mtomazella/Handy/BD/Diagrama/Handy.jpg

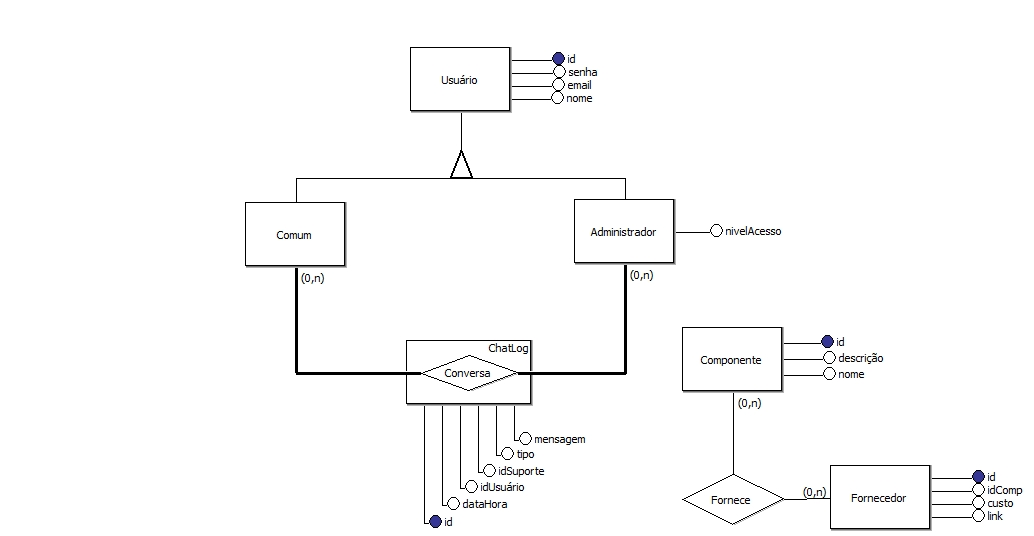
BD/Diagrama/Handy.jpg
