mtomazella/Handy/Documentação/Canvas/Canvas_-_Handy.vpd.png

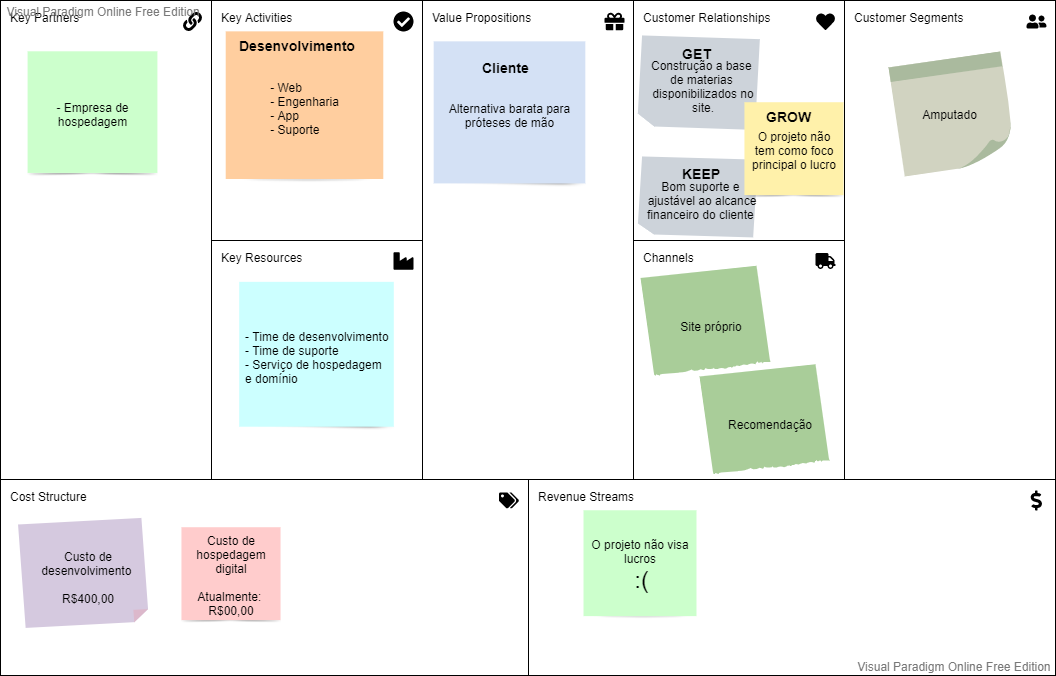
Documentação/Canvas/Canvas_-_Handy.vpd.png
