mtomazella/Handy/Documentação/Casos de Uso/Casos de Uso Mobile-Eng-1.jpg

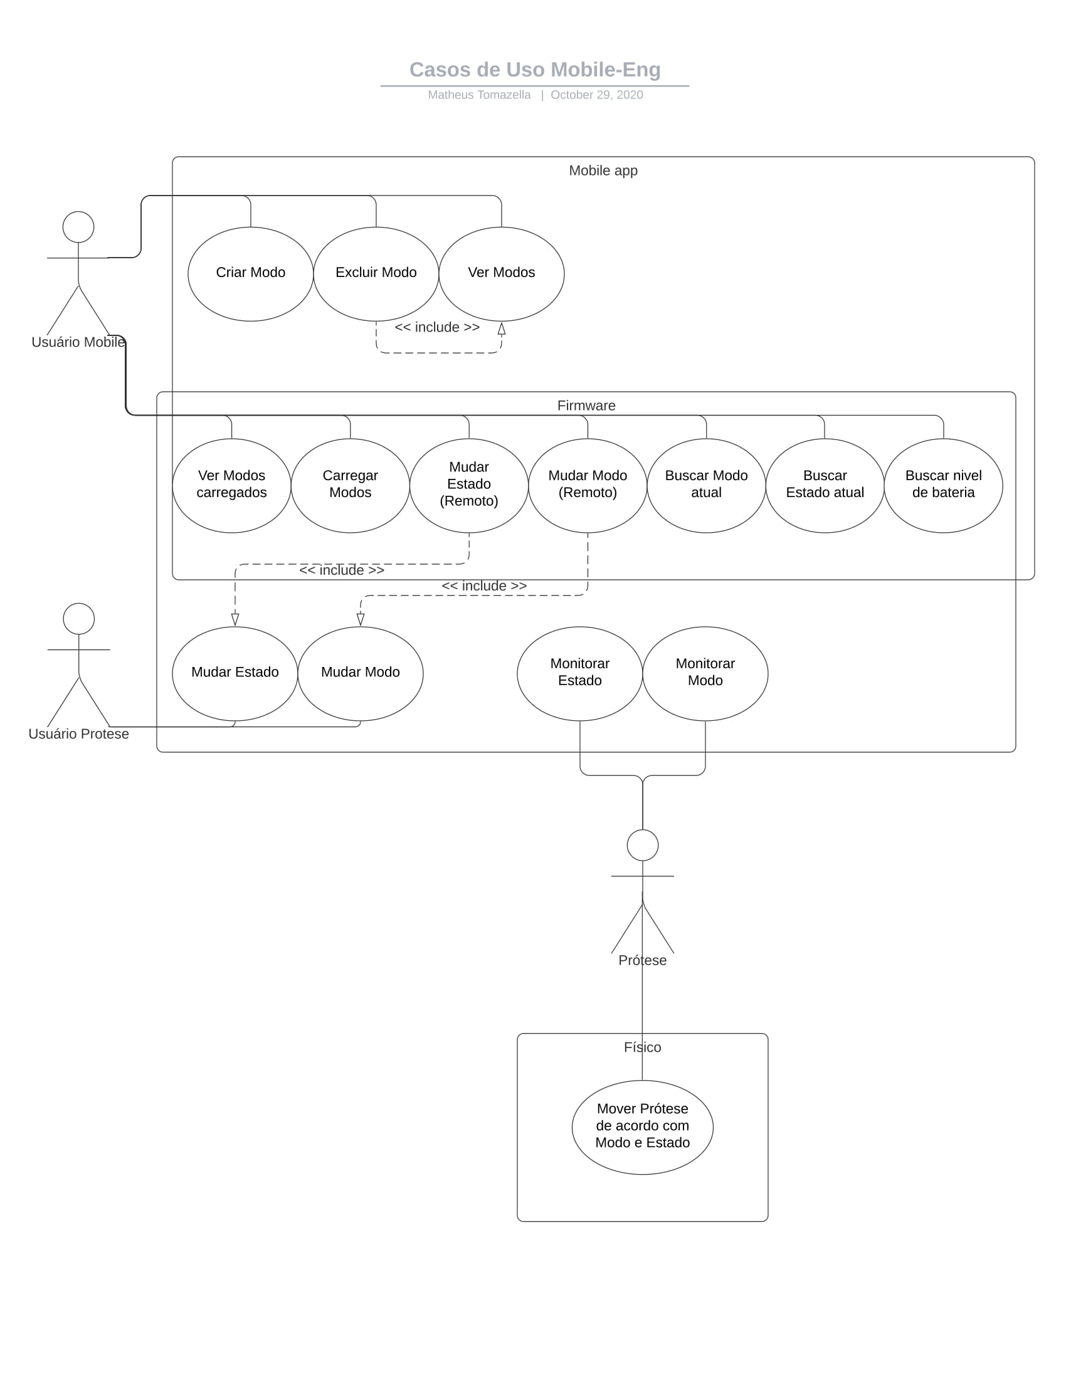
Documentação/Casos de Uso/Casos de Uso Mobile-Eng-1.jpg
