mtomazella/Handy/Documentação/Casos de Uso/Casos de Uso Web-Desktop-1.jpg

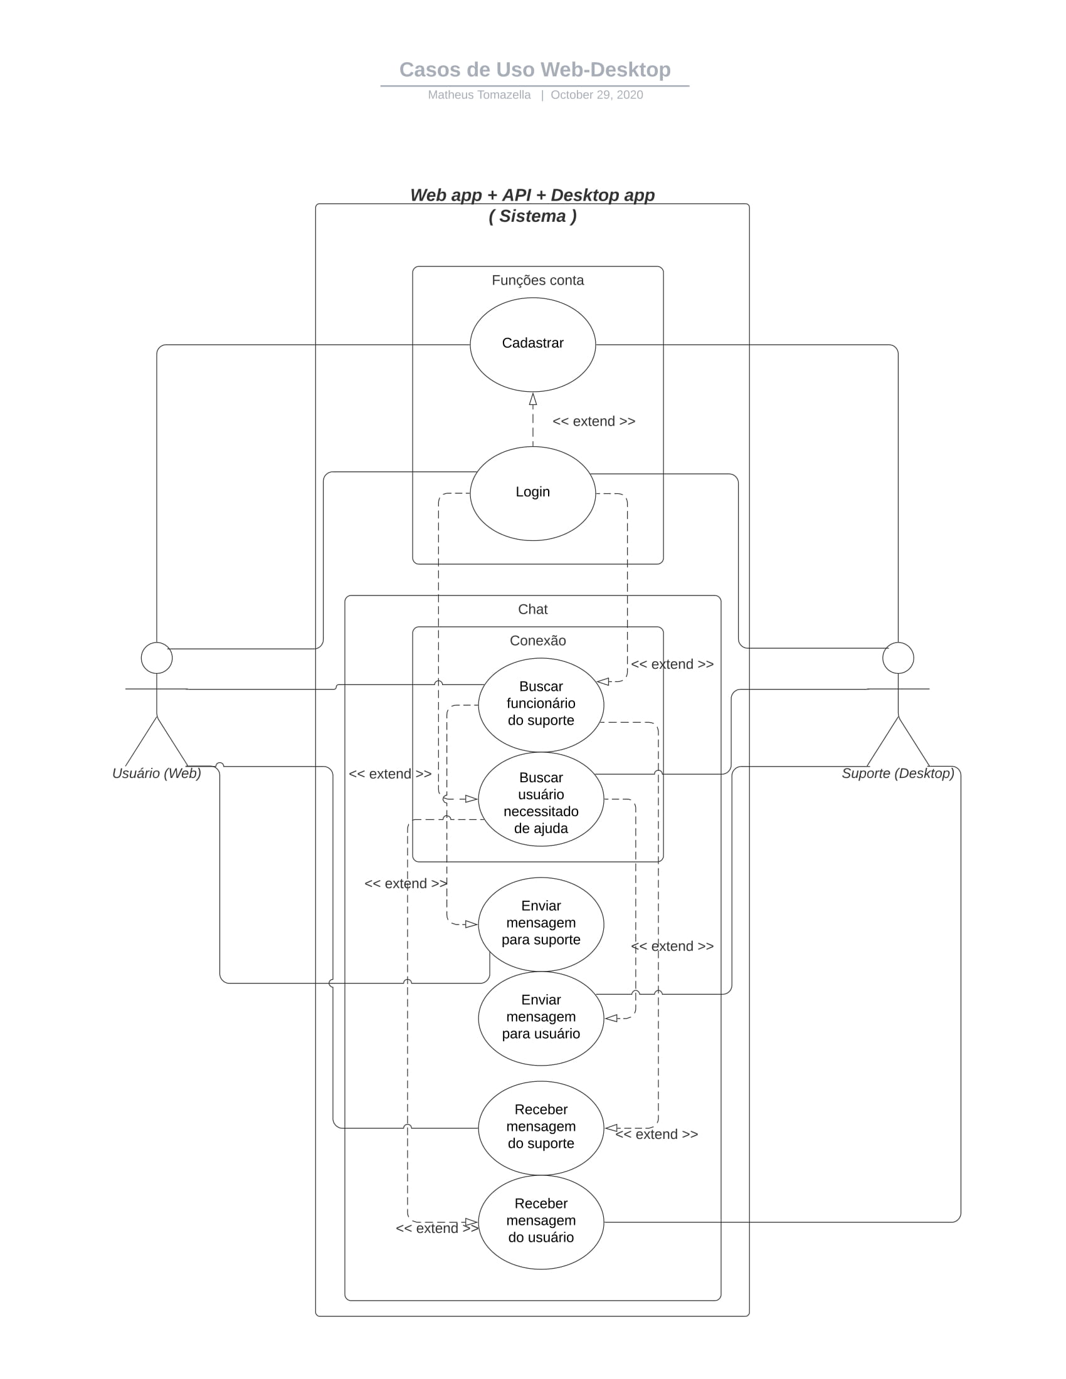
Documentação/Casos de Uso/Casos de Uso Web-Desktop-1.jpg
