mtomazella/Handy/Documentação/Cronograma/Cronograma.jpg

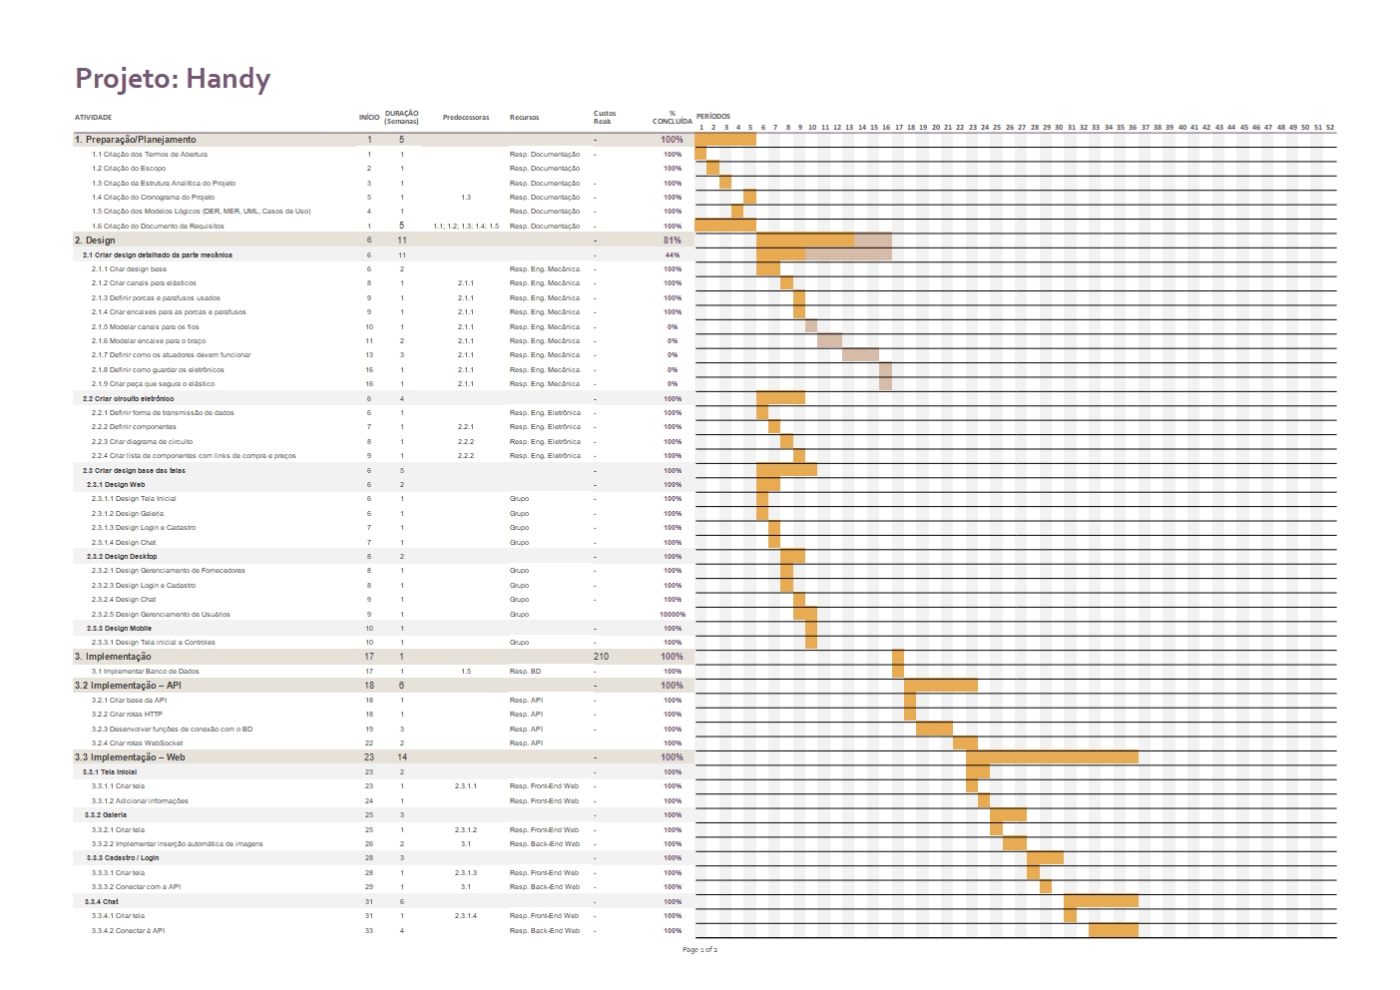
Documentação/Cronograma/Cronograma.jpg
