mtomazella/Handy/Documentação/Desenhos/Baterias.png

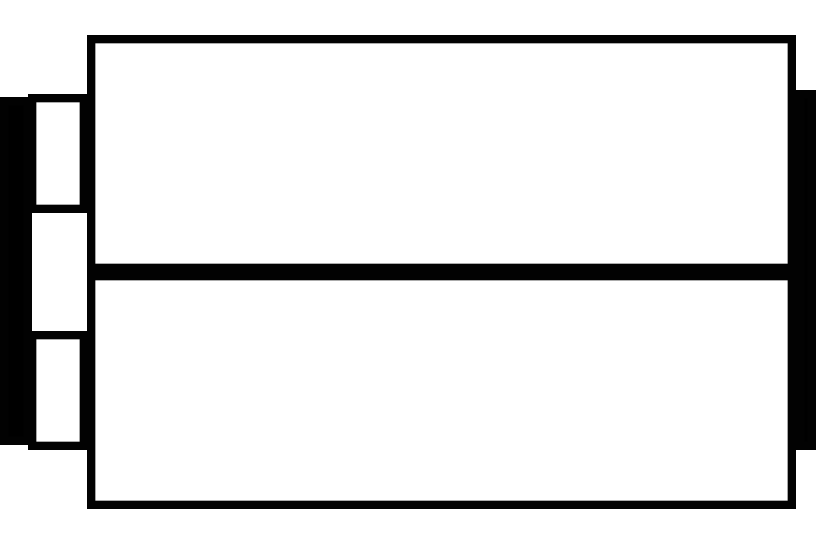
Documentação/Desenhos/Baterias.png
