mtomazella/Handy/Documentação/Desenhos/Handy.png

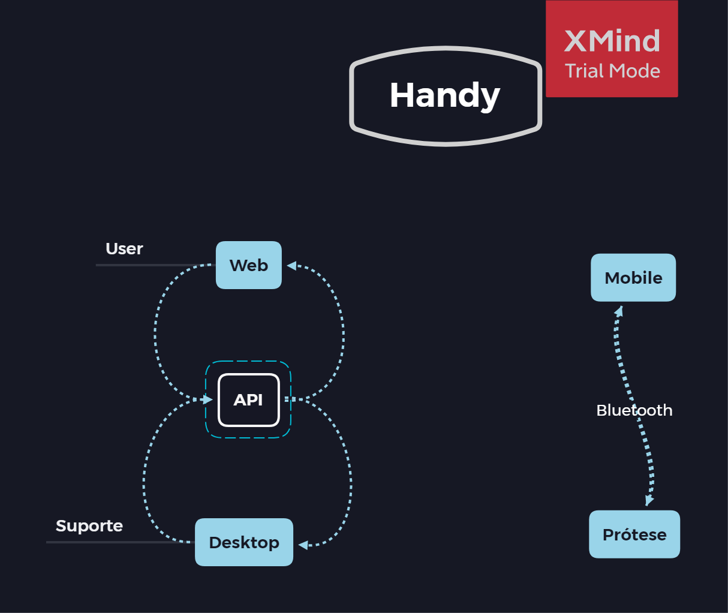
Documentação/Desenhos/Handy.png
