mtomazella/Handy/Documentação/Desenhos/PalmaSketch.png

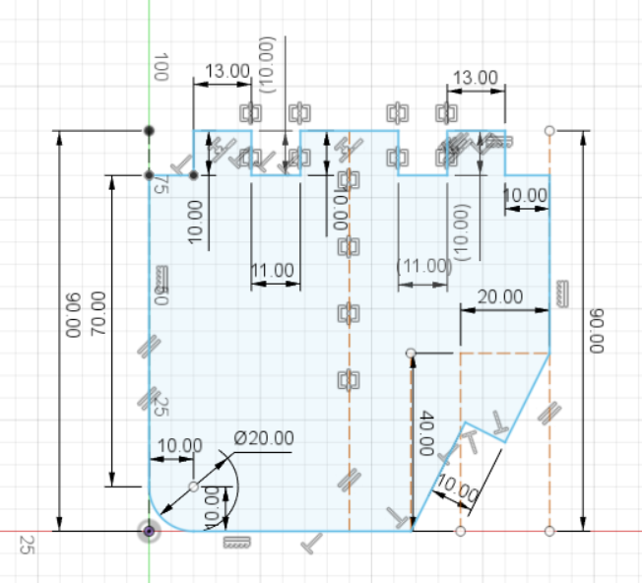
Documentação/Desenhos/PalmaSketch.png
