mtomazella/Handy/Documentação/EAP/EAP.png

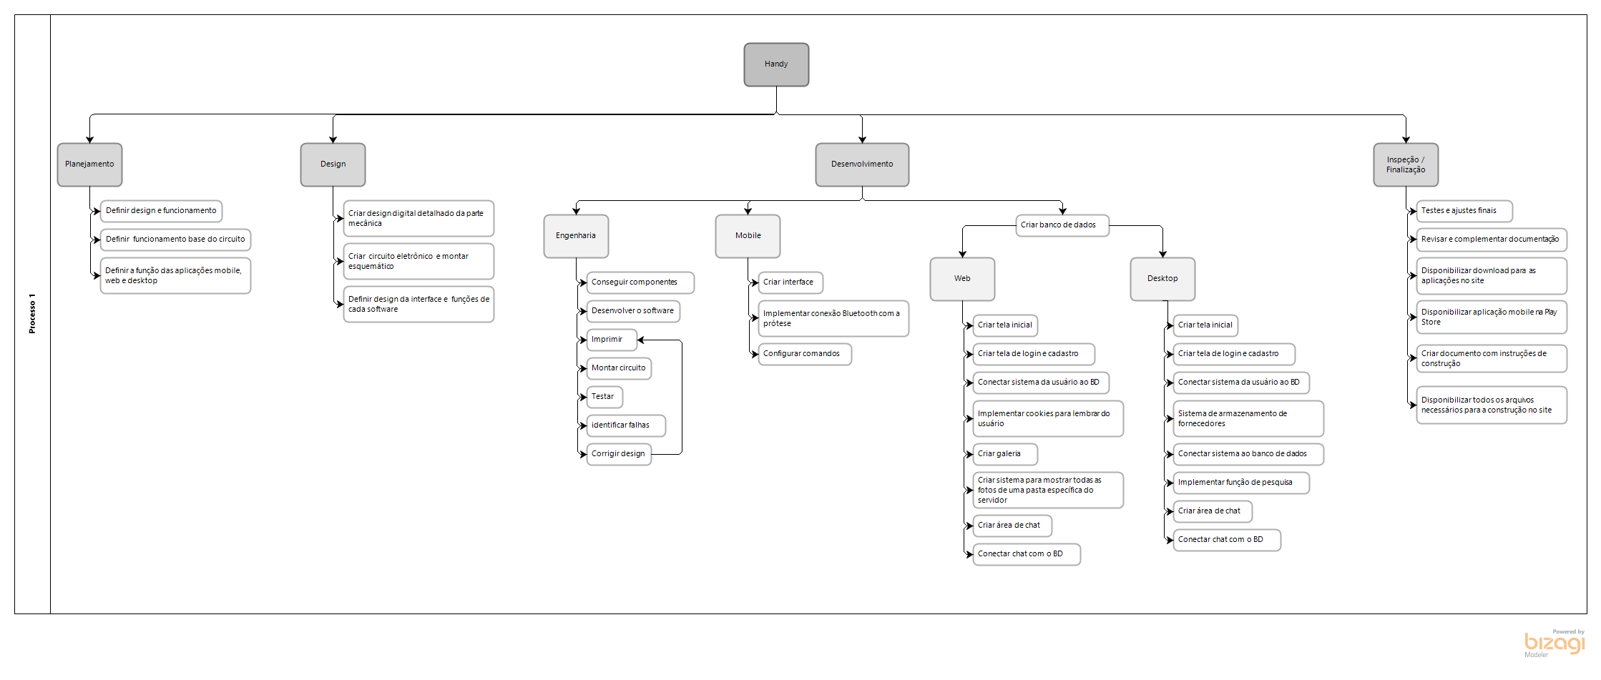
Documentação/EAP/EAP.png
