mtomazella/Handy/Documentação/EAP/Handy.png

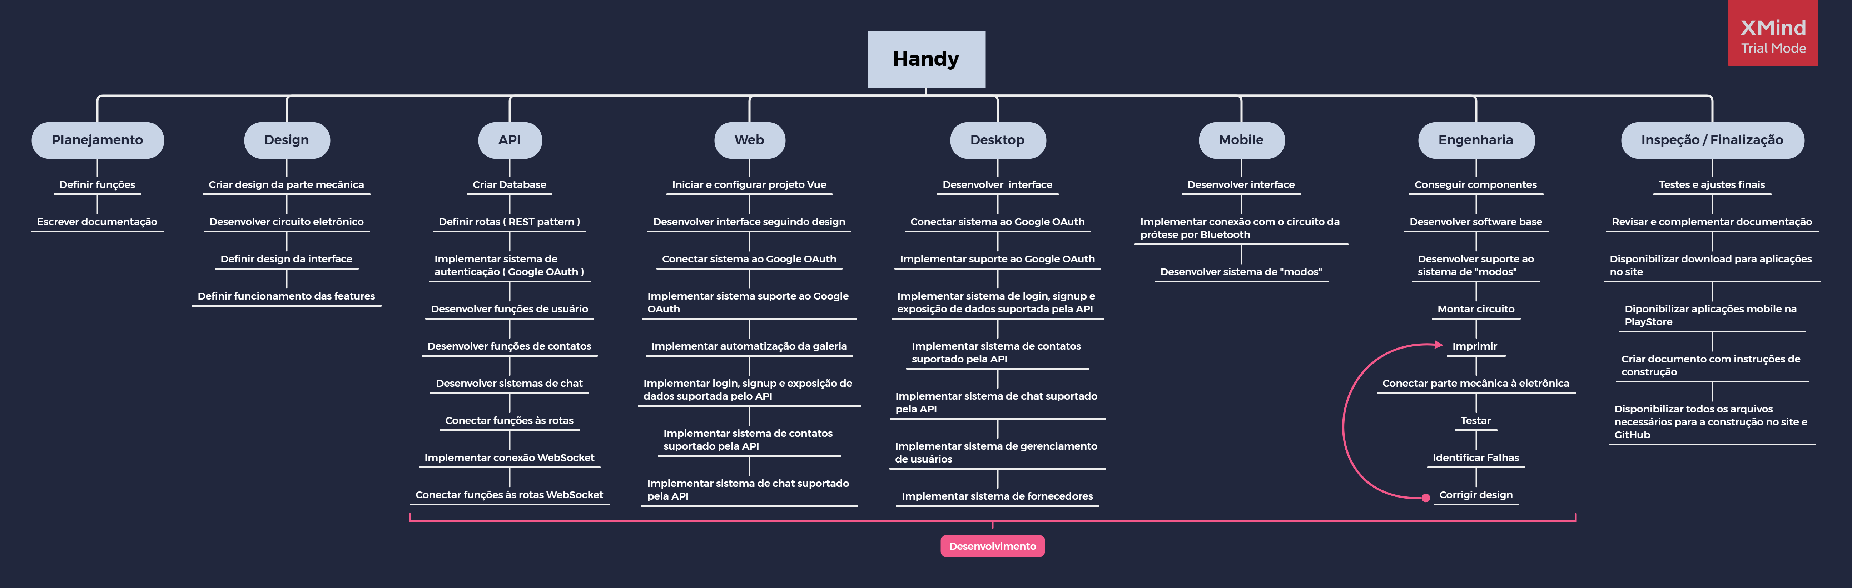
Documentação/EAP/Handy.png
