mtomazella/Handy/Eng/imgs/PróteseAberta.png

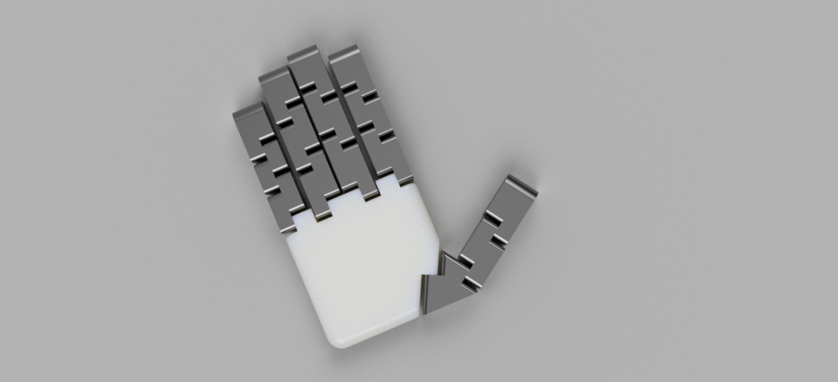
Eng/imgs/PróteseAberta.png
