mtomazella/Handy/Eng/imgs/PróteseFechada2.png

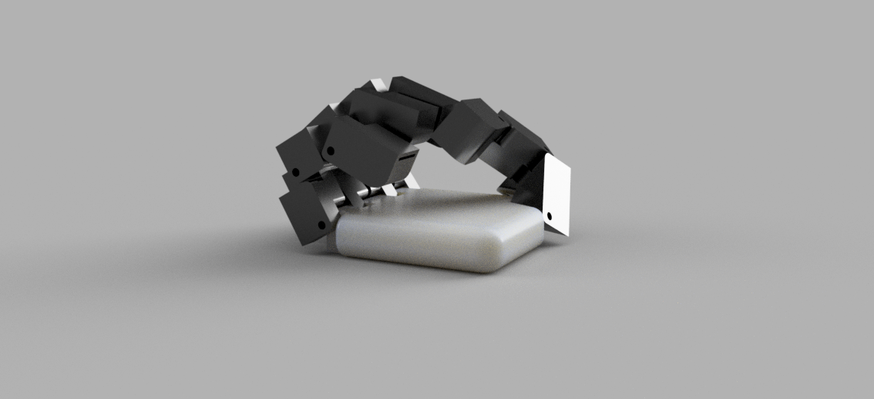
Eng/imgs/PróteseFechada2.png
