mtomazella/Handy/Eng/imgs/PróteseFechada.png

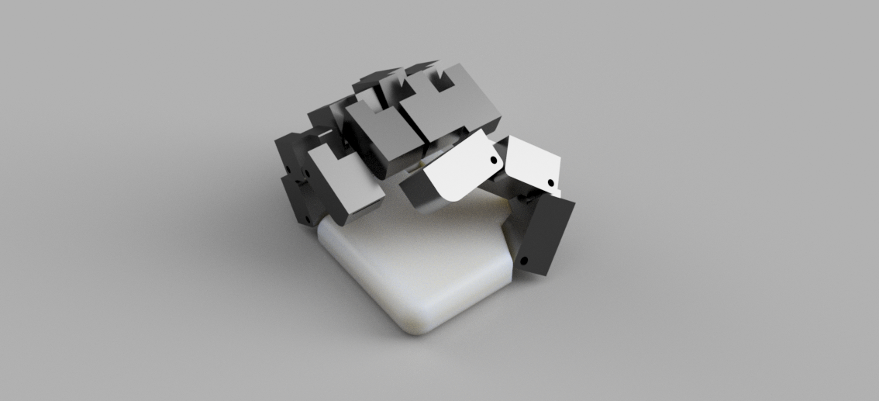
Eng/imgs/PróteseFechada.png
