mtomazella/Handy/Eng/imgs/PróteseFechadaCima.png

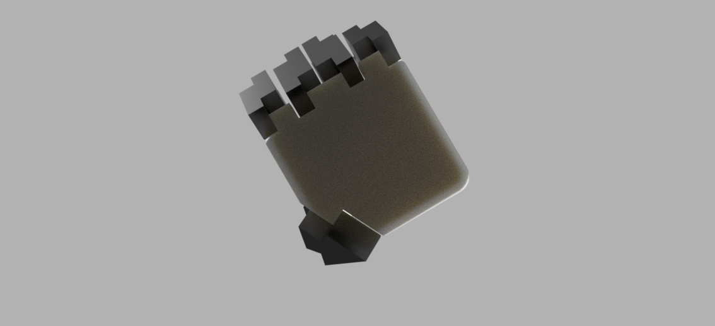
Eng/imgs/PróteseFechadaCima.png
