mtomazella/Handy/Eng/imgs/Render2020-06-26-1.jpg

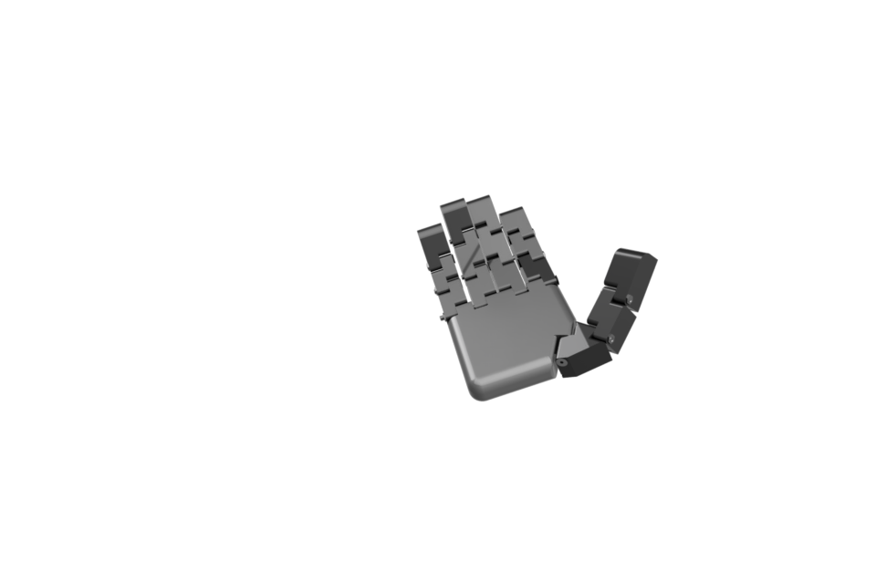
Eng/imgs/Render2020-06-26-1.jpg
