mtomazella/Handy/Eng/imgs/tccRenderCortado3.png

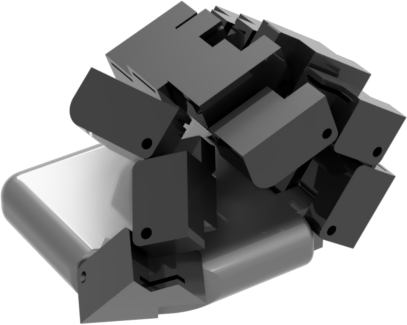
Eng/imgs/tccRenderCortado3.png
