mtomazella/Handy/Documentação/Desenhos/Parafuso Allen cabeça chata M4 20mm Drawing.pdf

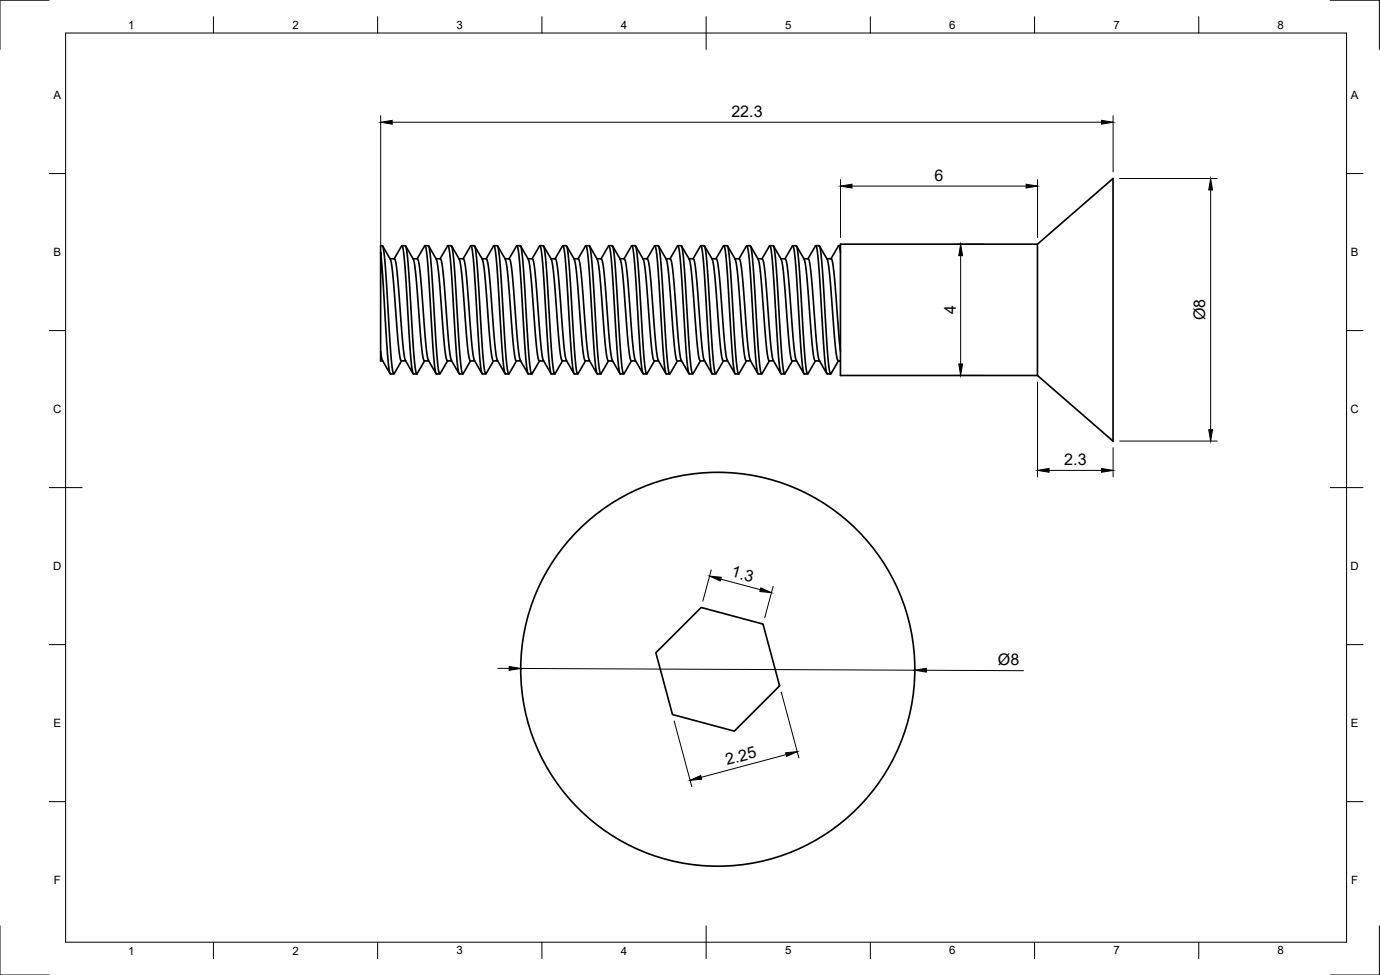
[picture p50: page 1]
8 BCDEF; ABCDEF
