mtomazella/Handy/Documentação/Desenhos/Parafuso Allen cabeça chata M4 26mm Drawing.pdf

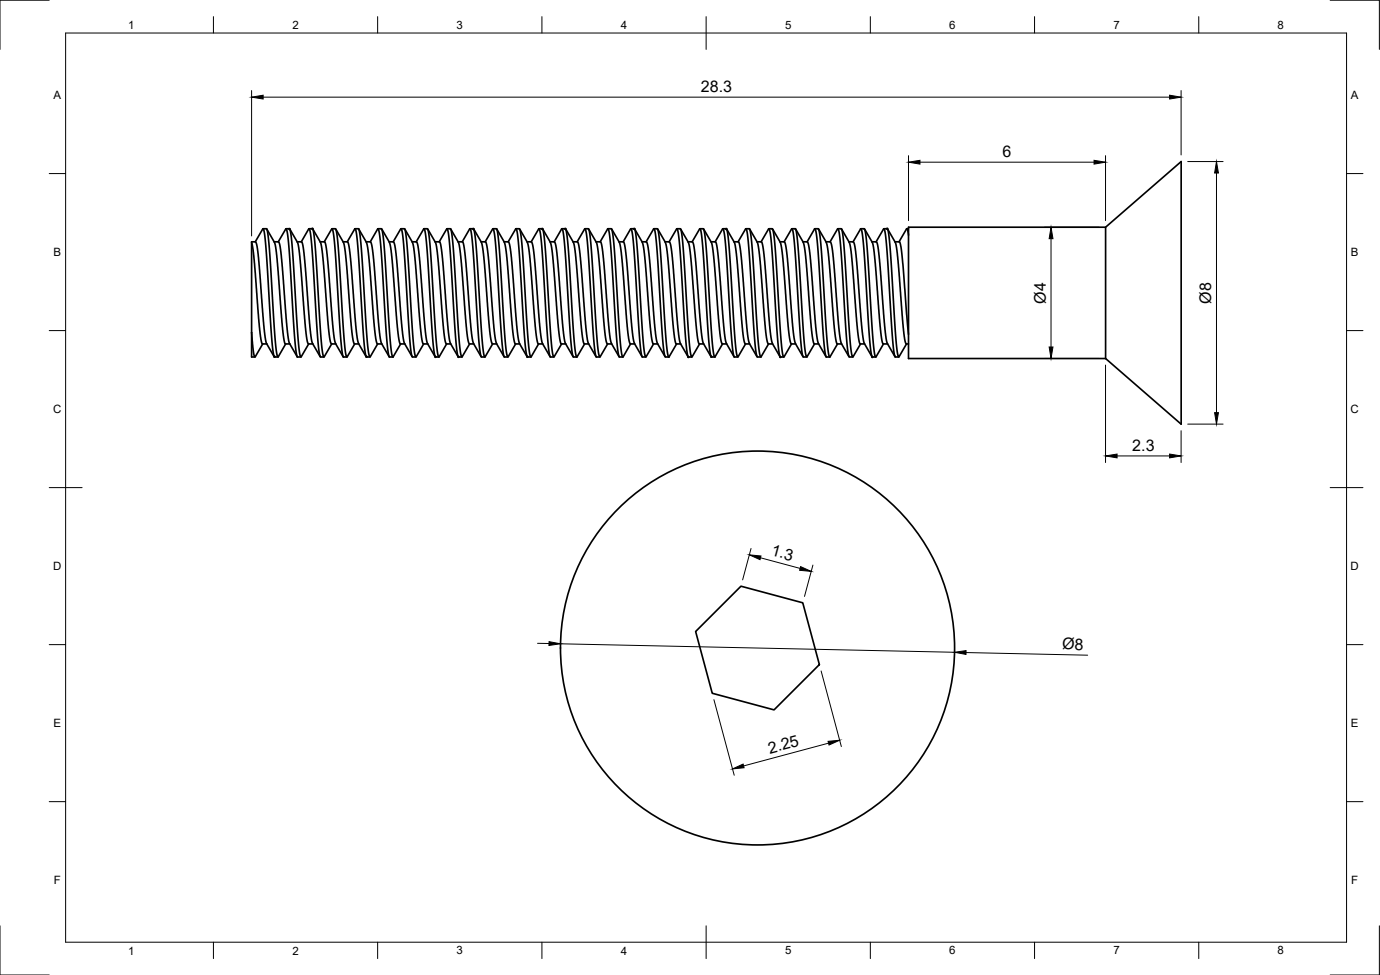
[picture p51: page 1]
8 BCDEF; ABCDEF 6
