mtomazella/Handy/Documentação/Desenhos/Parafuso Allen cabeça chata M4 90mm Drawing.pdf

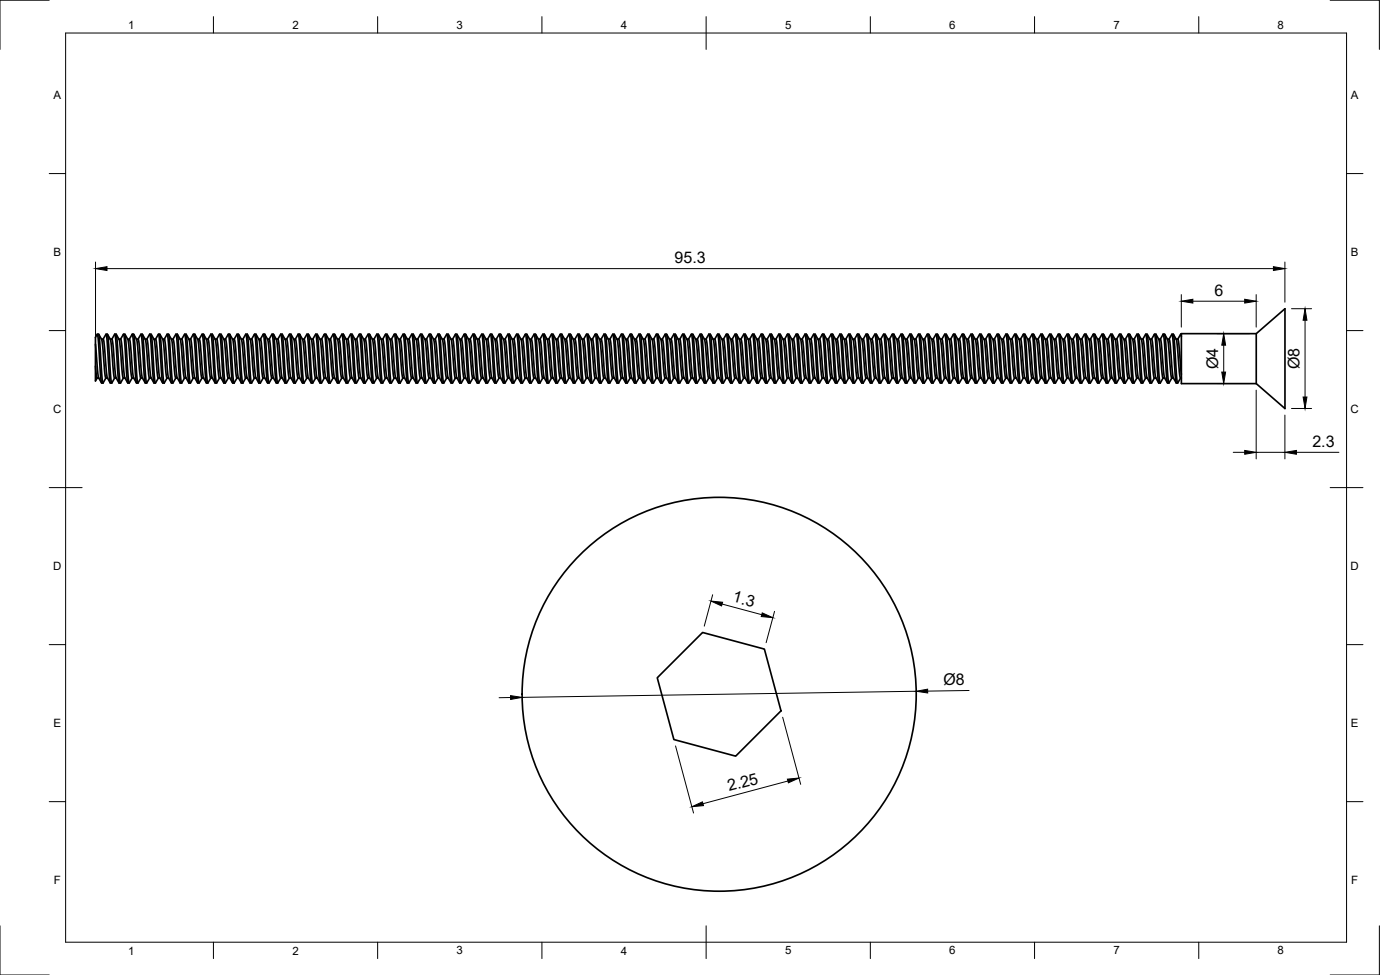
[picture p52: page 1]
8 BCDEF; ABCDEF Ø4
