mtomazella/Handy/Documentação/Desenhos/Porca M4 Drawing.pdf

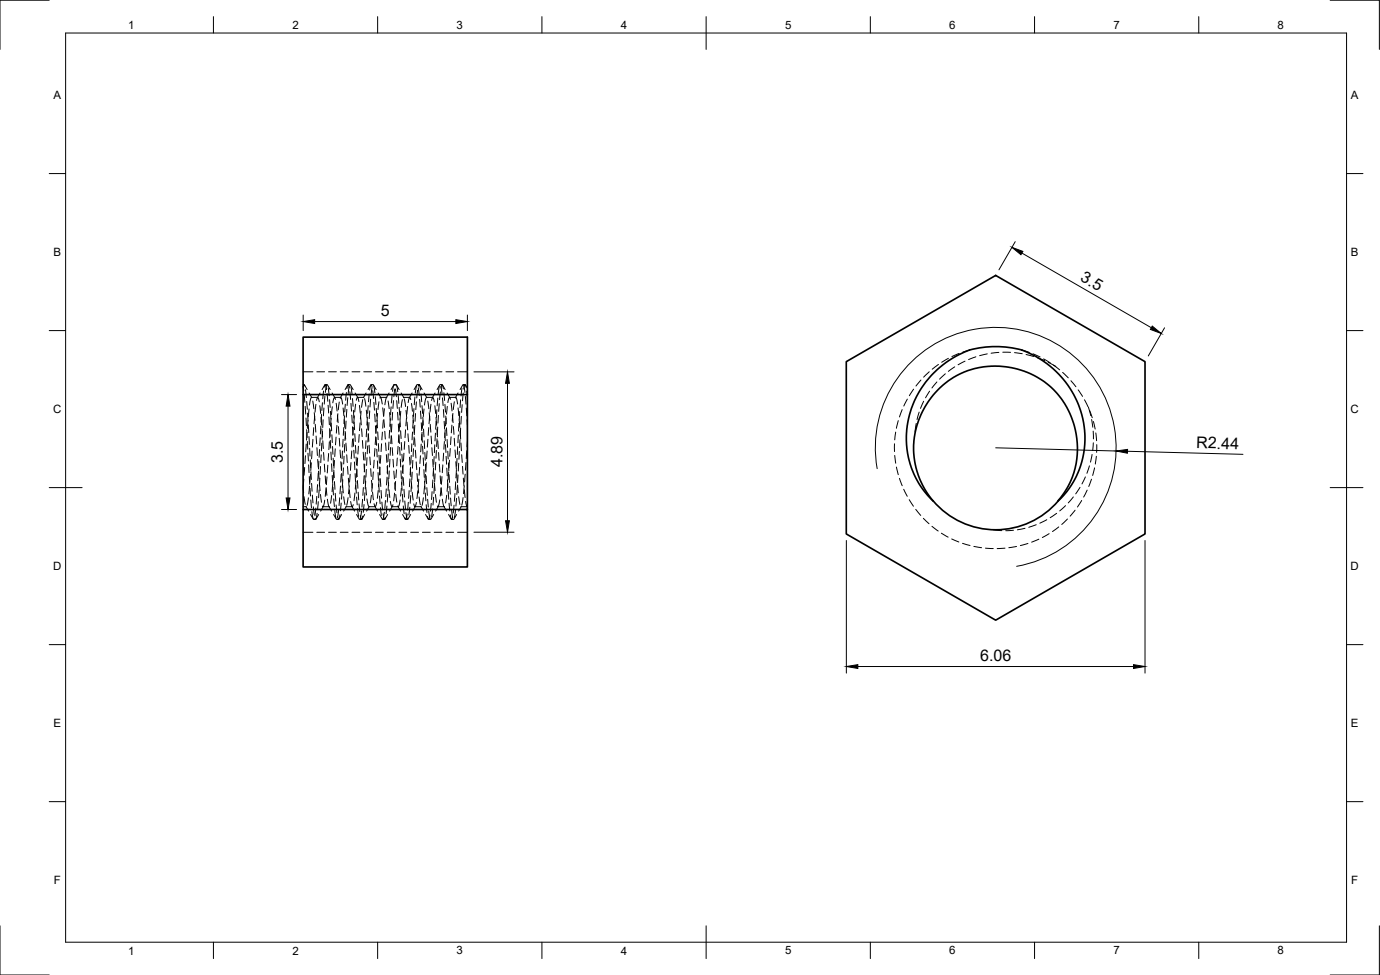
[picture p53: page 1]
8 BCDEF; ABCDEF 4.89 5 3.5
