mtomazella/Handy/Documentação/Desenhos/Prótese Drawing.pdf

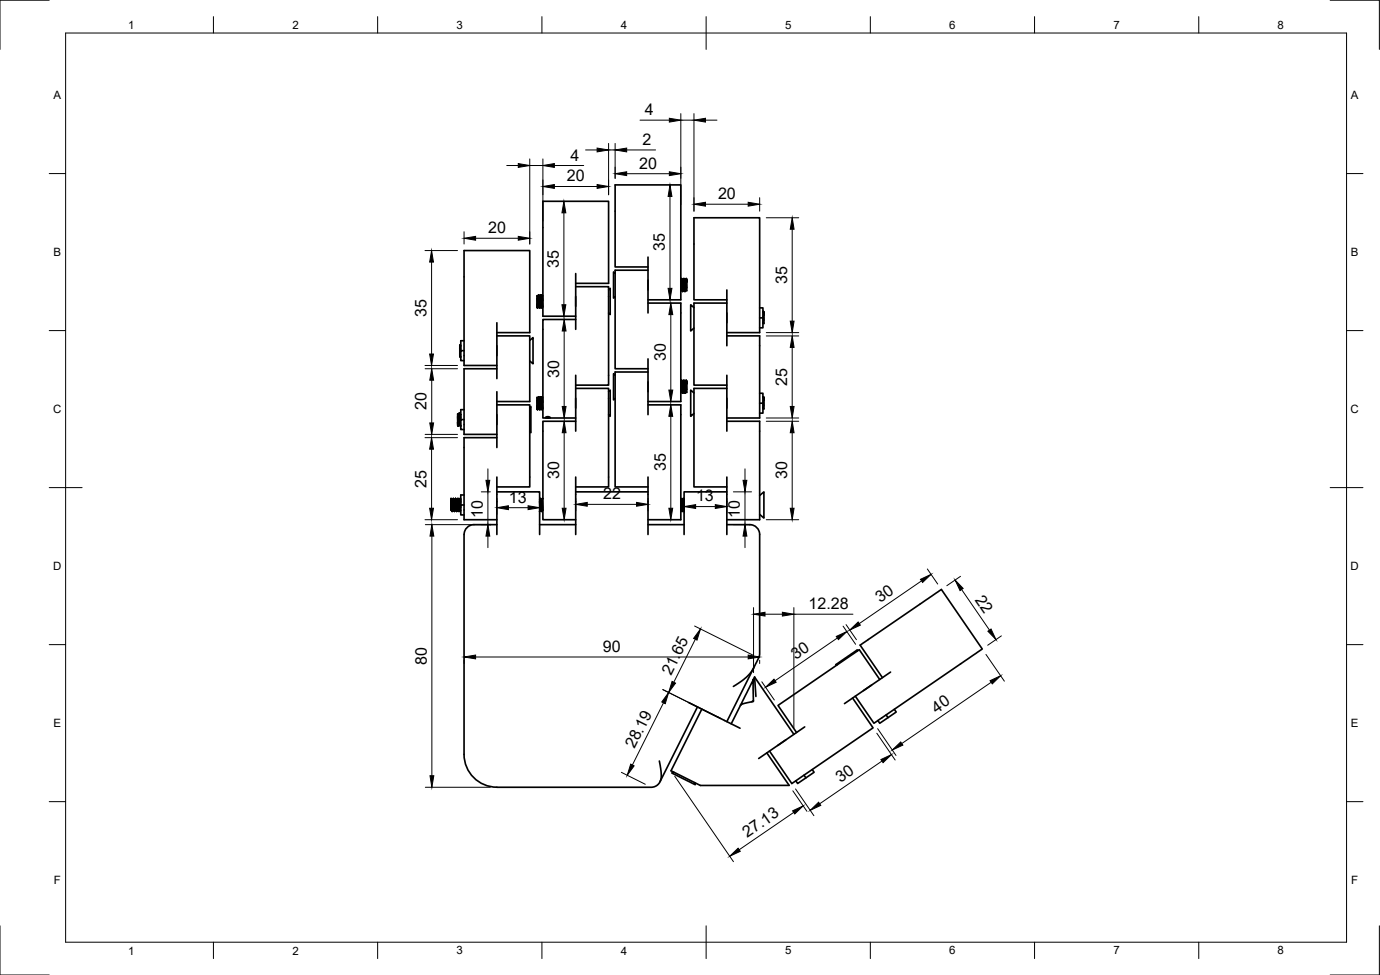
[picture p54: page 1]
8 BCDEF; ABCDEF 25 30

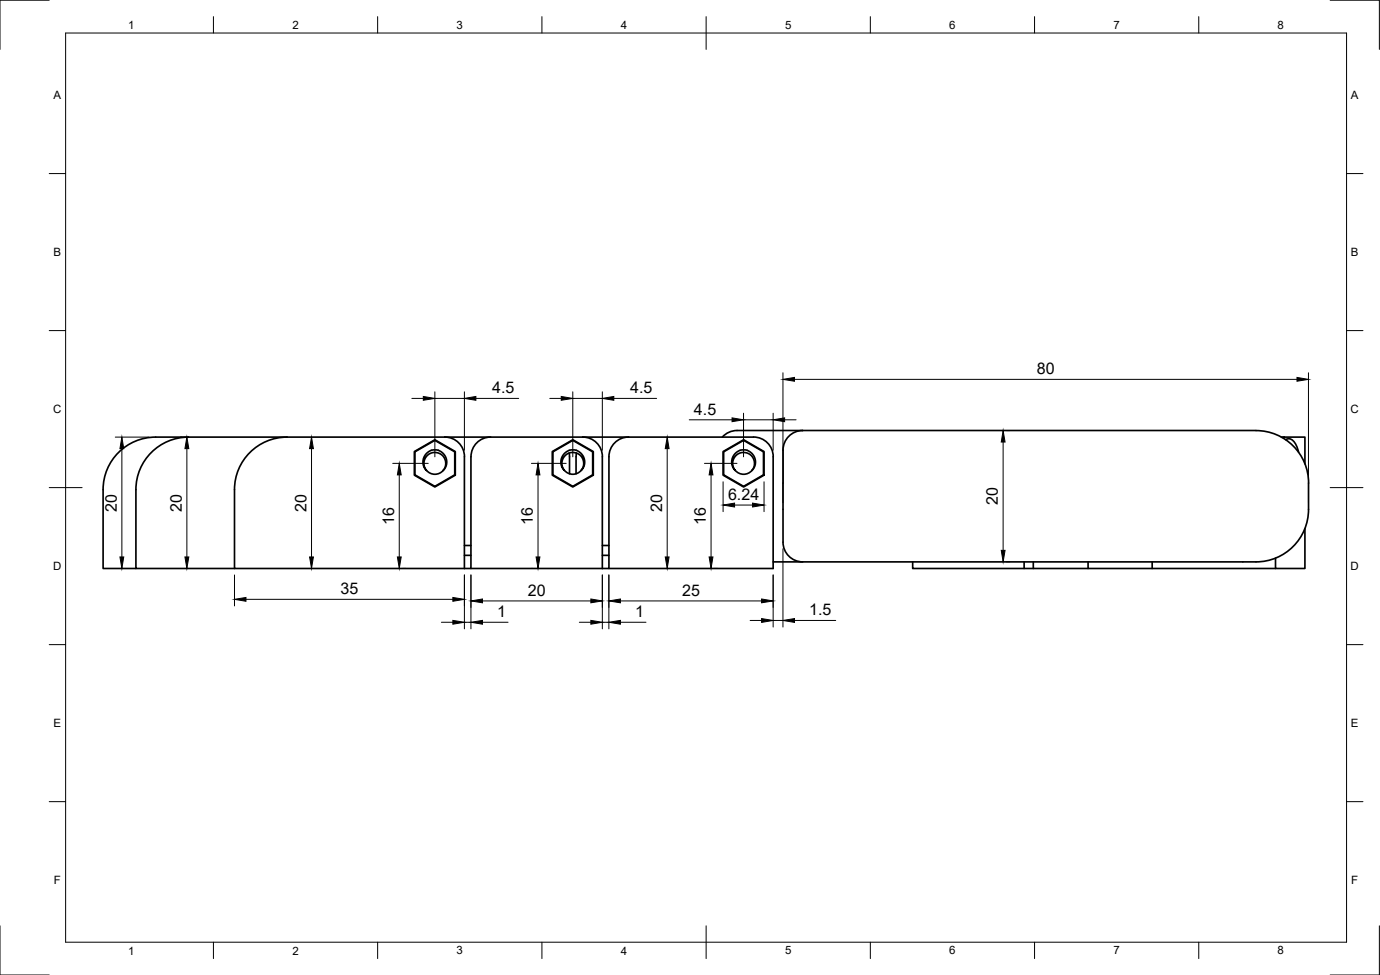
[picture p55: page 2]
